katascope/KataTracks/Images/LightDeviceMarkTwo-2.png

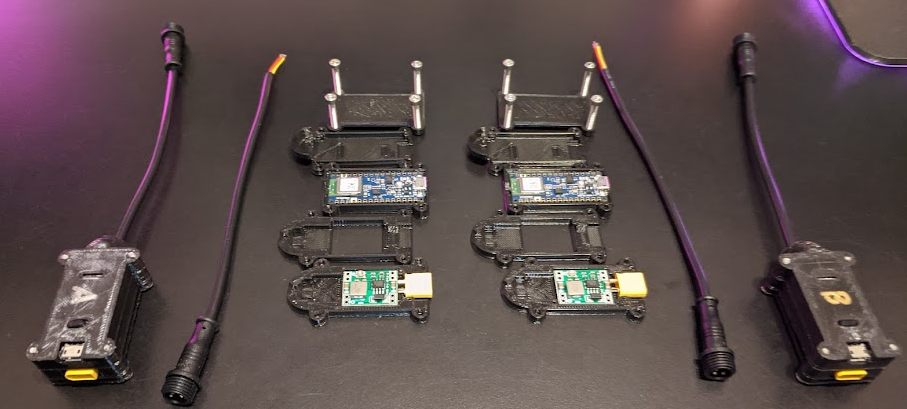
Images/LightDeviceMarkTwo-2.png
