katascope/KataTracks/Images/LightDevices.png

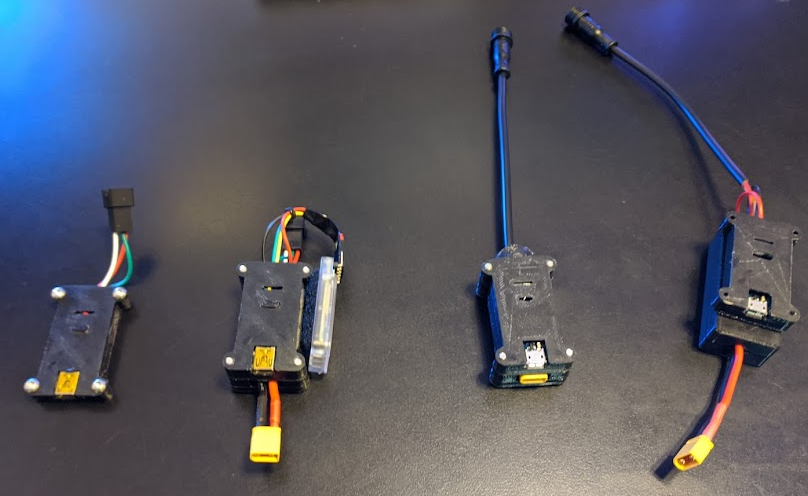
Images/LightDevices.png
