katascope/KataTracks/Images/PrototypeBluetooth2.png

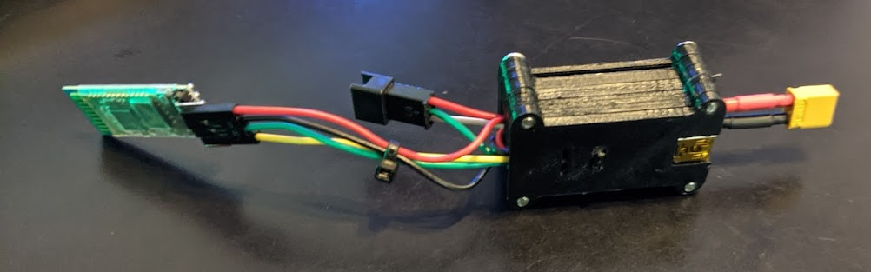
Images/PrototypeBluetooth2.png
