katascope/KataTracks/Images/PrototypeJacket1.png

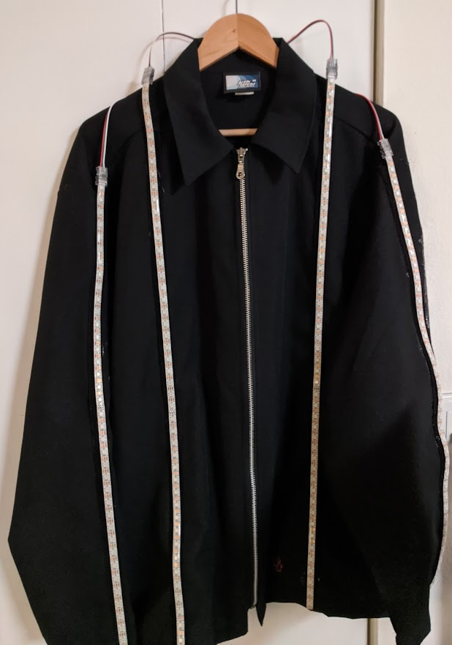
Images/PrototypeJacket1.png
