katascope/KataTracks/KataTracks/TronGame.png

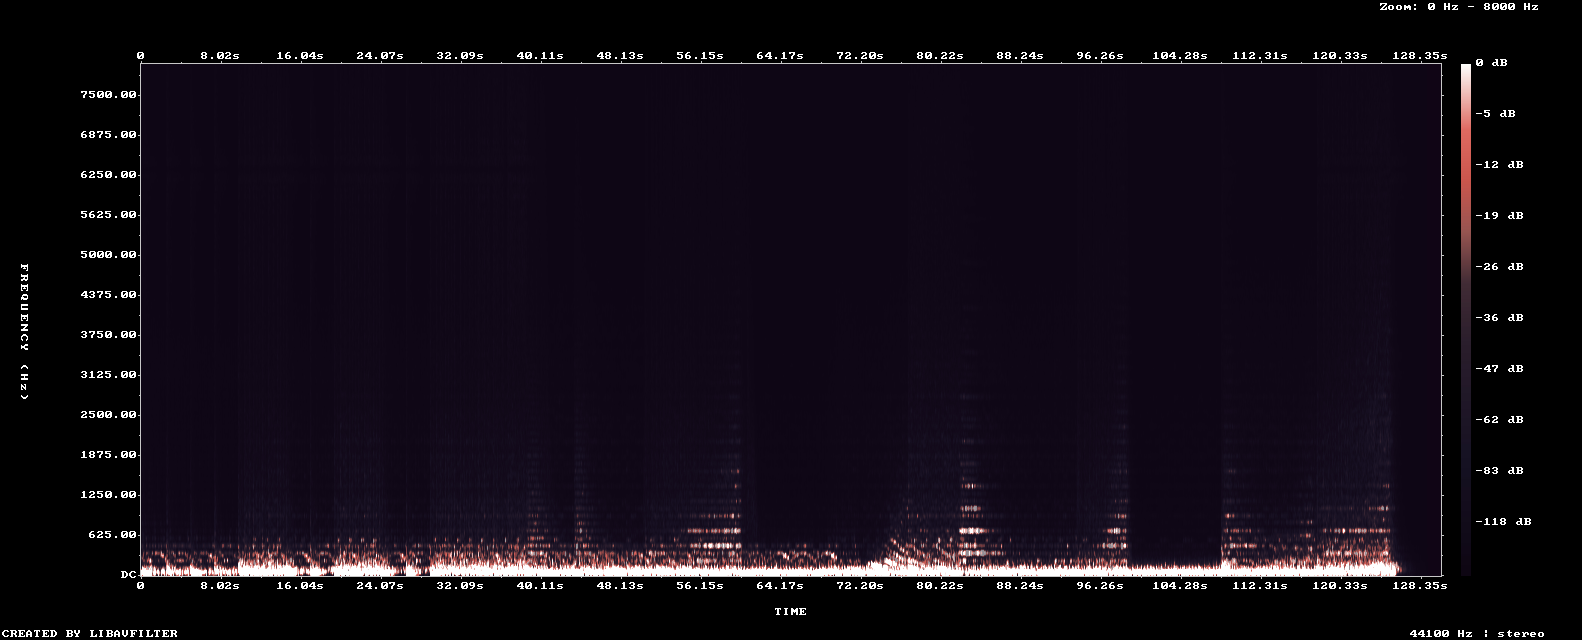
KataTracks/TronGame.png
