katascope/KataTracks/KataTracks/TronGameCropped.png

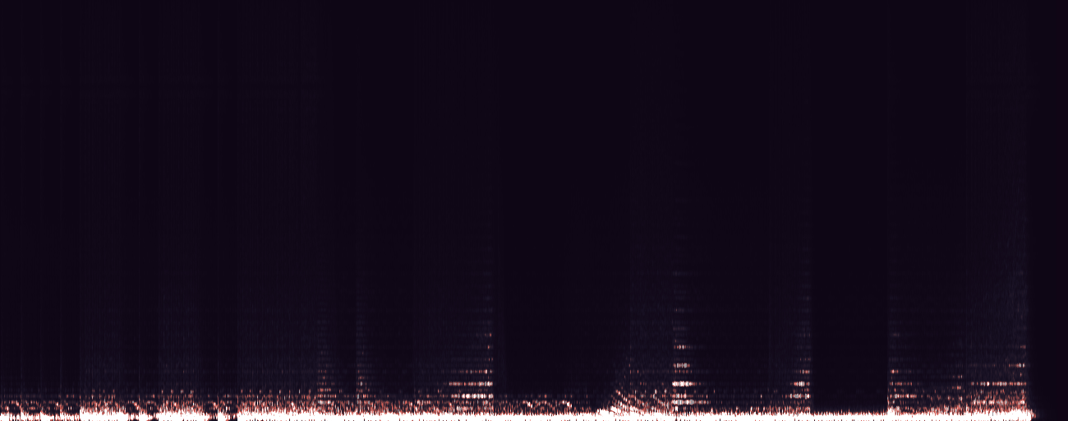
KataTracks/TronGameCropped.png
