katascope/KataTracks/KataTracks/TronGameCroppedCyan.png

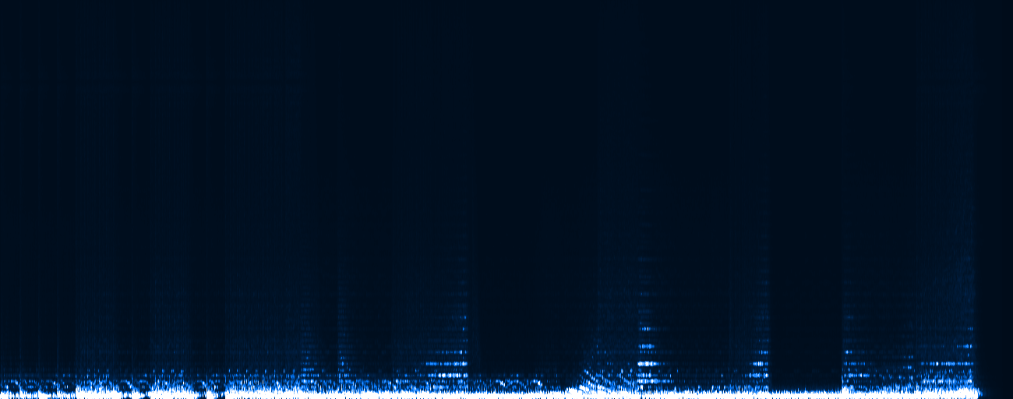
KataTracks/TronGameCroppedCyan.png
