katascope/KataTracks/LedTracks/Commands.cpp

#include "Commands.h"
#include "Fx.h"
#include "Track.h"
#include "Timecode.h"
#if ENABLE_NEOPIXEL
#include "NeoPixel.h"
#endif

void UpdatePalette();
unsigned long GetTime();

static CaptureTextMode captureMode = CaptureNone;
static uint32_t palette16[16] = {0, 0, 0, 0, 0, 0, 0, 0, 0, 0, 0, 0, 0, 0, 0, 0};
static char captureBuffer[16] = {0, 0, 0, 0, 0, 0, 0, 0, 0, 0, 0, 0, 0, 0, 0, 0};
static int captureCount = 0;

void InstantEvent(FxController &fxc, int event, bool setUpdatePalette)
{
  fxc.updatePalette = setUpdatePalette;
  fxc.fxState = FxState_Default;
  fxc.transitionType = Transition_Instant;
  if (event != fx_nothing)
    PrintFxEventName(event);
  FxEventProcess(fxc, event);
  UpdatePalette();
}

void magicColors(FxController &fxc, int count)
{
  int index = 0;
  for (int i=0;i<16;i++)
  {
    char c = captureBuffer[index];
    uint32_t crgb = ShortnameToCRGB(c);
    palette16[i] = crgb;
    index++;
    if (index > count) index = 0;  
  }

  CreatePaletteBands(fxc,
    palette16[0],  palette16[1],  palette16[2],  palette16[3], 
    palette16[4],  palette16[5],  palette16[6],  palette16[7], 
    palette16[8],  palette16[9],  palette16[10], palette16[11], 
    palette16[12], palette16[13], palette16[14], palette16[15]);
 
  //InstantEvent(fxc, fx_nothing, true);
  UpdatePalette(); 
}

void UserCommandExecute(FxController &fxc, int cmd)
{
  switch (cmd)
  {
    case Cmd_Help:
      Serial.println(F("? : Help Menu"));
      Serial.println(F("+ : Rotate Pos"));
      Serial.println(F("- : Rotate Neg"));
      Serial.println(F("( : Track Start"));
      Serial.println(F(") : Track Stop"));
      Serial.println(F("* : Track StartFrom"));
      Serial.println(F("!code : Color code"));
      Serial.println(F("@code : Time code"));
      Serial.println(F("z:default mode x:test c:imu"));
      Serial.println(F("0:dark 1:white 2:red 3:yellow 4:green 5:cyan 6:blue 7:magenta 8:orange 9:half"));
      Serial.println(F("q:lava w:cloud e:ocean r:forest t:rainbow y:rainbowstripe u:party i:heat"));
      break;
    case Cmd_State_Default: fxc.fxState = FxState_Default;break;
    case Cmd_State_Test:    fxc.fxState = FxState_TestPattern;break;
    case Cmd_State_IMU:     fxc.fxState = FxState_IMU;break;
      
    case Cmd_PlayFromStart: trackStart(fxc, 0, (unsigned long)(millis() - (signed long)TRACK_START_DELAY), fxc.trackEndAction); break;
    case Cmd_PlayFrom:      fxc.fxState = FxState_PlayingTrack;break;
    case Cmd_PlayStop:      trackStop(fxc); break;

    case Cmd_SpeedNeg:      InstantEvent(fxc, fx_speed_neg, true); break;
    case Cmd_SpeedPos:      InstantEvent(fxc, fx_speed_pos, true); break;
    case Cmd_SpeedDec:      InstantEvent(fxc, fx_speed_dec, true); break;
    case Cmd_SpeedInc:      InstantEvent(fxc, fx_speed_inc, true); break;
    case Cmd_SpeedRst:      InstantEvent(fxc, fx_speed_0, true); break;
    
    case Cmd_ColorDark:     InstantEvent(fxc, fx_palette_dark, false); break;
    case Cmd_ColorWhite:    InstantEvent(fxc, fx_palette_white, false); break;
    case Cmd_ColorRed:      InstantEvent(fxc, fx_palette_red, false); break;
    case Cmd_ColorYellow:   InstantEvent(fxc, fx_palette_yellow, false); break;
    case Cmd_ColorGreen:    InstantEvent(fxc, fx_palette_green, false); break;
    case Cmd_ColorCyan:     InstantEvent(fxc, fx_palette_cyan, false); break;
    case Cmd_ColorBlue:     InstantEvent(fxc, fx_palette_blue, false); break;
    case Cmd_ColorMagenta:  InstantEvent(fxc, fx_palette_magenta, false); break;
    case Cmd_ColorOrange:   InstantEvent(fxc, fx_palette_orange, false); break;
    case Cmd_ColorHalf:     InstantEvent(fxc, fx_palette_half, false); break;

    case Cmd_ColorLava:           InstantEvent(fxc, fx_palette_lava, true); break;
    case Cmd_ColorCloud:          InstantEvent(fxc, fx_palette_cloud, true); break;
    case Cmd_ColorOcean:          InstantEvent(fxc, fx_palette_ocean, true); break;
    case Cmd_ColorForest:         InstantEvent(fxc, fx_palette_forest, true); break;
    case Cmd_ColorRainbow:        InstantEvent(fxc, fx_palette_rainbow, true); break;
    case Cmd_ColorRainbowstripe:  InstantEvent(fxc, fx_palette_rainbowstripe, true); break;
    case Cmd_ColorParty:          InstantEvent(fxc, fx_palette_party, true); break;
    case Cmd_ColorHeat:           InstantEvent(fxc, fx_palette_heat, true); break;

#if ENABLE_NEOPIXEL && ENABLE_BRIGHTNESS
    case Cmd_Brightness_VeryHigh: neopixelSetBrightness(250);break;
    case Cmd_Brightness_High: neopixelSetBrightness(150);break;
    case Cmd_Brightness_Normal: neopixelSetBrightness(50);break;
    case Cmd_Brightness_Low: neopixelSetBrightness(20);break;
#endif    

    default: break;
  }
}

void processCapturedText(FxController &fxc)
{
  if (captureMode == CaptureColorCode)
  {  
    Serial.print(F("ColorDef("));
    Serial.print(captureCount);
    Serial.print(F(")=("));
    for (int i = 0; i < captureCount; i++)
    {
      Serial.print((char)captureBuffer[i]);
    }
    Serial.print(F(")"));
    Serial.println();

    //Magic colors is currently broken as it breaks serial print for some unknown reason
    magicColors(fxc,captureCount);
    captureCount = 0;
    captureMode = CaptureNone;
  }
  else if (captureMode == CaptureTimeCode)
  { 
    captureMode = CaptureNone;
    unsigned long tc = atoi(captureBuffer);
    int prevmatch = GetPreviousTimeCodeMatch(tc);    
    setTimecodeLastMatched(SongTrack_timecode(prevmatch));
    setTimecodeSongOffset(tc);  
    Serial.print(F("TC:"));
    Serial.print(tc);
    Serial.print(F(" vs t="));
    Serial.print(GetTime());
    Serial.print(F(", to="));
    Serial.print(getTimecodeTimeOffset());
    setTimecodeTimeOffset(millis());
    Serial.print(F(", "));
    Serial.print(getTimecodeLastMatched());
    Serial.print(F("="));
    Serial.print(getTimecodeSongOffset());
    Serial.print(F(",P:"));
    Serial.print(prevmatch);
    Serial.println(F(""));

    trackStart(fxc,tc, (unsigned long)(millis() - (signed long)TRACK_START_DELAY), FxTrackEndAction::StopAtEnd);
  }
}

void UserCommandInput(FxController &fxc, int data)
{
  if (captureMode == CaptureColorCode && data != 10 && data != 13)
  {
    if (captureCount < 16)
    {
      captureBuffer[captureCount] = (char)data;
      captureCount++;
    }
    return;
  }   

  if (captureMode == CaptureTimeCode && data != 10 && data != 13)
  {
    if (captureCount < 15)
    {
      captureBuffer[captureCount] = (char)data;
      captureBuffer[captureCount+1] = 0;
      captureCount++;
    }
    return;
  }

  switch (data)
  {
    case '!':
      //PrintLogln(F("Capturing ColorCode"));
      captureCount = 0;
      captureMode = CaptureColorCode;
      break;
    case '@':
      //PrintLogln(F("Capturing TimeCode"));
      captureCount = 0;
      //capturedTimeCode = "";
      captureMode = CaptureTimeCode;
      break;
    case '?': UserCommandExecute(fxc, Cmd_Help); break;
      
    case 'z': UserCommandExecute(fxc, Cmd_State_Default);break;
    case 'x': UserCommandExecute(fxc, Cmd_State_Test);break;
    case 'c': UserCommandExecute(fxc, Cmd_State_IMU);break;      
    
    case ')': UserCommandExecute(fxc, Cmd_PlayFromStart); break;
    case '*': UserCommandExecute(fxc, Cmd_PlayFrom); break;
    case '(': UserCommandExecute(fxc, Cmd_PlayStop); break;
    
    case '0': UserCommandExecute(fxc, Cmd_ColorDark); break;
    case '1': UserCommandExecute(fxc, Cmd_ColorWhite); break;
    case '2': UserCommandExecute(fxc, Cmd_ColorRed); break;
    case '3': UserCommandExecute(fxc, Cmd_ColorYellow); break;
    case '4': UserCommandExecute(fxc, Cmd_ColorGreen); break;
    case '5': UserCommandExecute(fxc, Cmd_ColorCyan); break;
    case '6': UserCommandExecute(fxc, Cmd_ColorBlue); break;
    case '7': UserCommandExecute(fxc, Cmd_ColorMagenta); break;
    case '8': UserCommandExecute(fxc, Cmd_ColorOrange); break;
    case '9': UserCommandExecute(fxc, Cmd_ColorHalf); break;
    
    case 'q': UserCommandExecute(fxc, Cmd_ColorLava);break;
    case 'w': UserCommandExecute(fxc, Cmd_ColorCloud);break;
    case 'e': UserCommandExecute(fxc, Cmd_ColorOcean);break;
    case 'r': UserCommandExecute(fxc, Cmd_ColorForest);break;
    case 't': UserCommandExecute(fxc, Cmd_ColorRainbow);break;
    case 'y': UserCommandExecute(fxc, Cmd_ColorRainbowstripe);break;
    case 'u': UserCommandExecute(fxc, Cmd_ColorParty);break;
    case 'i': UserCommandExecute(fxc, Cmd_ColorHeat);break;

    case '_': UserCommandExecute(fxc, Cmd_SpeedNeg);break;
    case '+': UserCommandExecute(fxc, Cmd_SpeedPos);break;
    case '-': UserCommandExecute(fxc, Cmd_SpeedDec);break;
    case '=': UserCommandExecute(fxc, Cmd_SpeedInc);break;
    case '~': UserCommandExecute(fxc, Cmd_SpeedRst);break;

    case 'b': UserCommandExecute(fxc, Cmd_Brightness_High);break;
    case 'n': UserCommandExecute(fxc, Cmd_Brightness_Normal);break;
    case 'm': UserCommandExecute(fxc, Cmd_Brightness_Low);break;
    case ',': UserCommandExecute(fxc, Cmd_Brightness_VeryHigh);break;
    
    case 10:
    case 13:
      if (captureMode != CaptureNone)
        processCapturedText(fxc);
    case 0:
    case 225: break;
    default:
      Serial.print(F("unk:"));
      Serial.println(data);
      break;
  }
}
